sstojos/zynthian-mini/resources/assembled_top.png

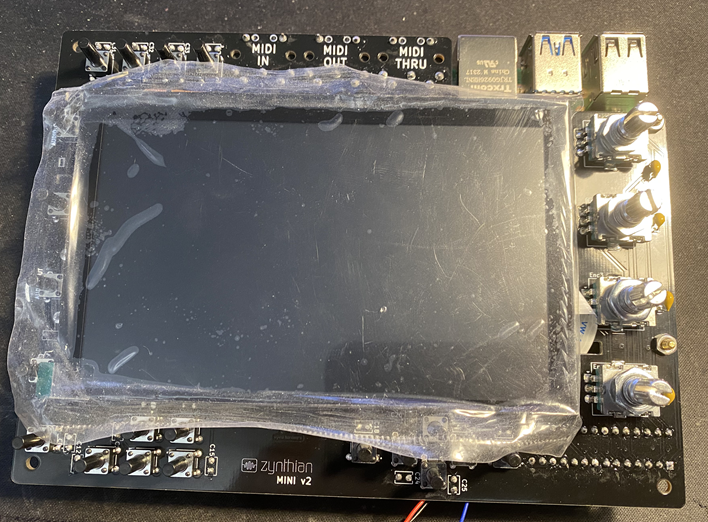
resources/assembled_top.png
