sstojos/zynthian-mini/resources/new-case-layout.png

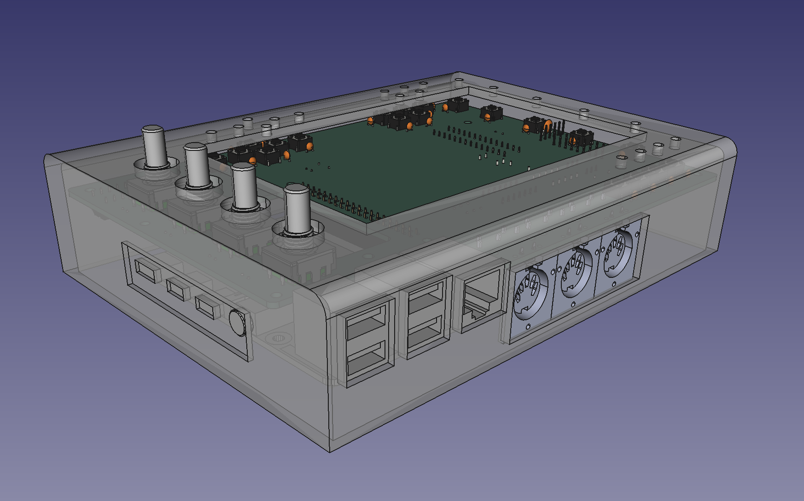
resources/new-case-layout.png
