sstojos/zynthian-mini/resources/PCB-back-with-rpi.png

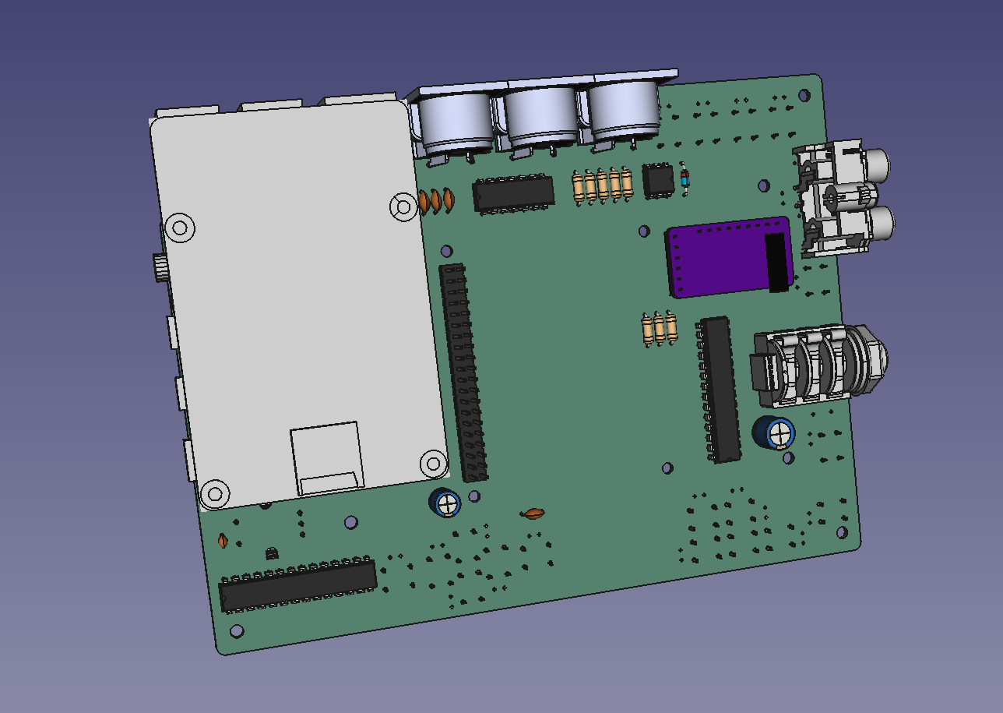
resources/PCB-back-with-rpi.png
