sstojos/zynthian-mini/resources/PCB-back.png

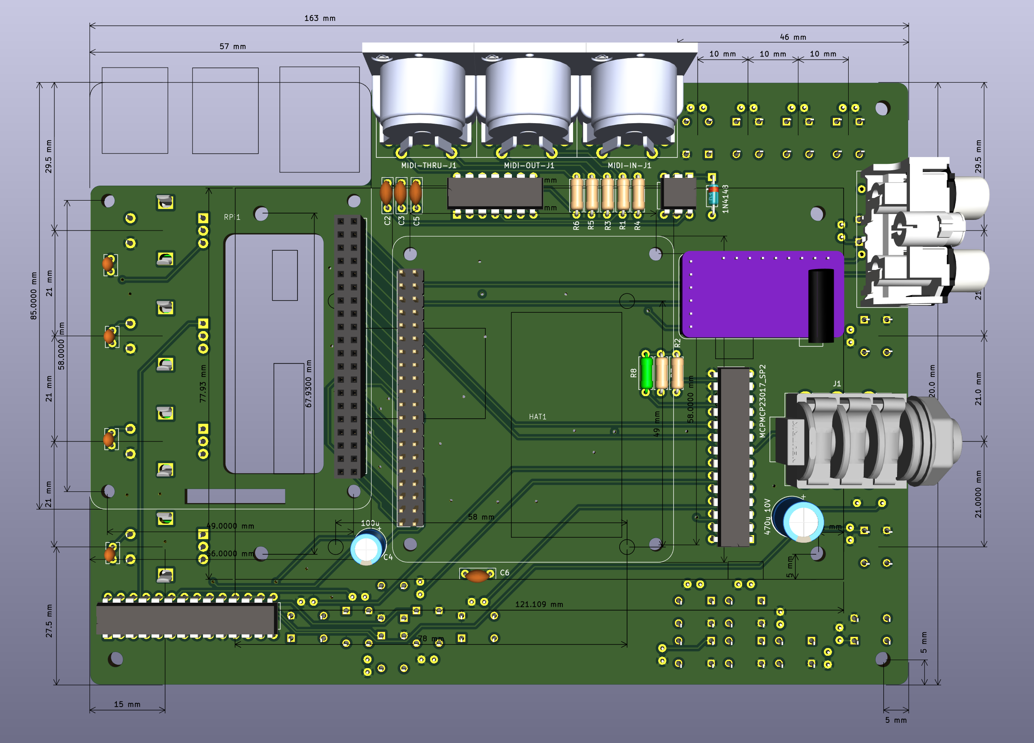
resources/PCB-back.png
