sstojos/zynthian-mini/resources/PCB-front.png

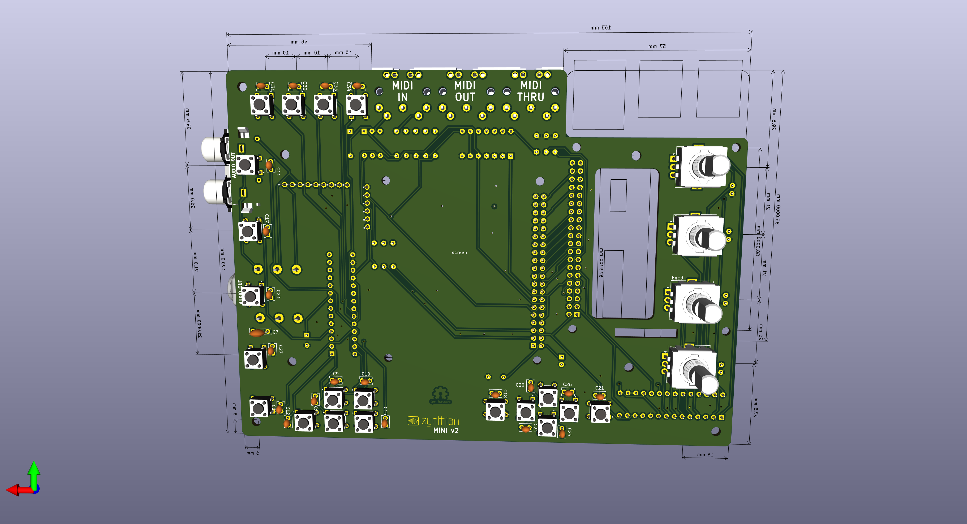
resources/PCB-front.png
