sstojos/zynthian-mini/resources/pcm5102a_circuit_diagram-1.webp

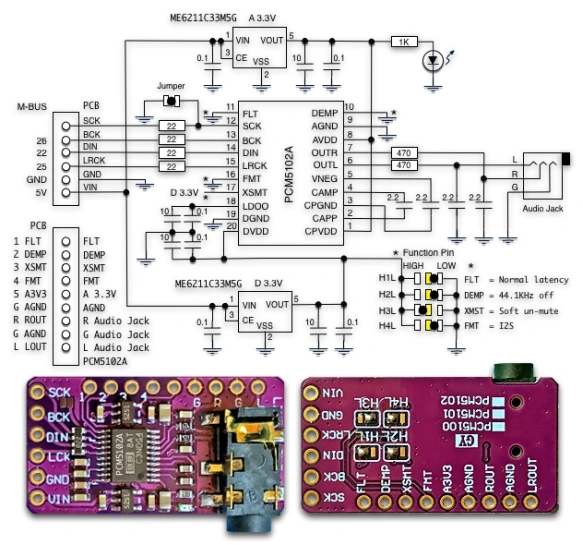
resources/pcm5102a_circuit_diagram-1.webp
