sstojos/zynthian-mini/resources/rpi-cooler.png

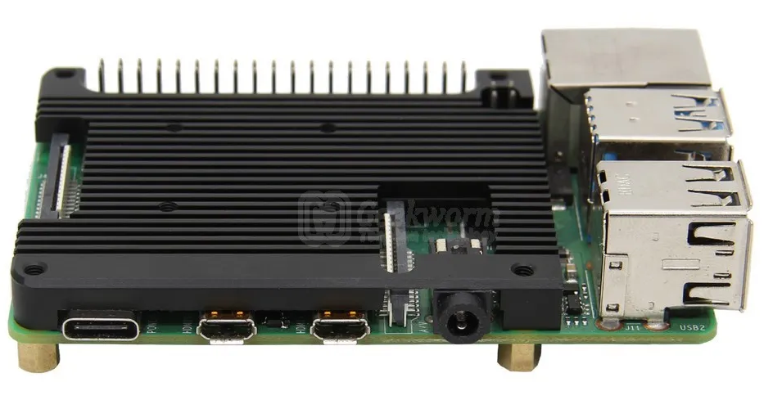
resources/rpi-cooler.png
