sstojos/zynthian-mini/resources/rpi_screen_cable.png

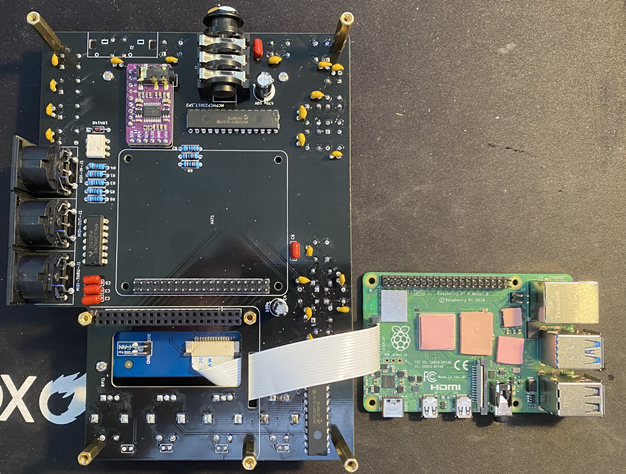
resources/rpi_screen_cable.png
