sstojos/zynthian-mini/resources/screen_cable.png

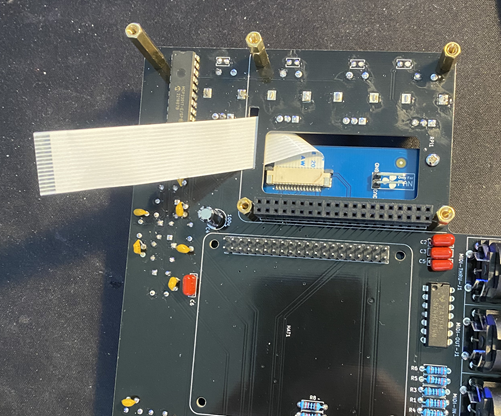
resources/screen_cable.png
