sstojos/zynthian-mini/resources/screen_post_removal.png

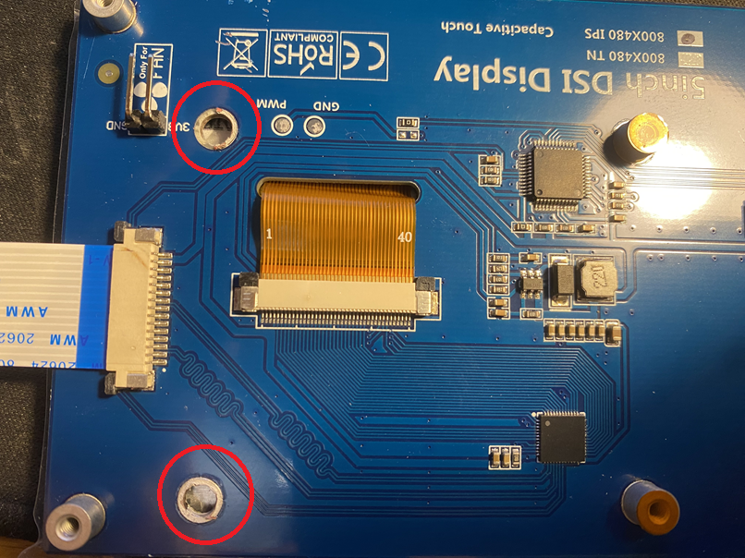
resources/screen_post_removal.png
