sstojos/zynthian-mini/resources/slicer-screenshot-01.png

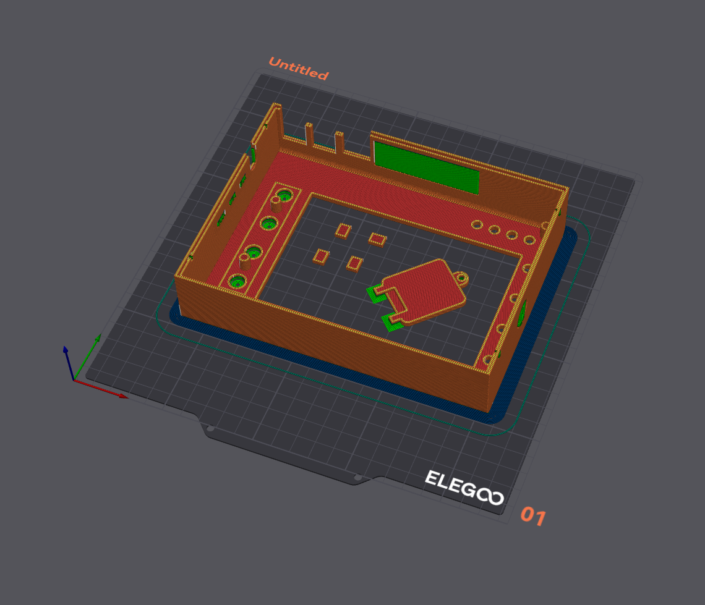
resources/slicer-screenshot-01.png
