sstojos/zynthian-mini/resources/zynthian-on-piano-01.png

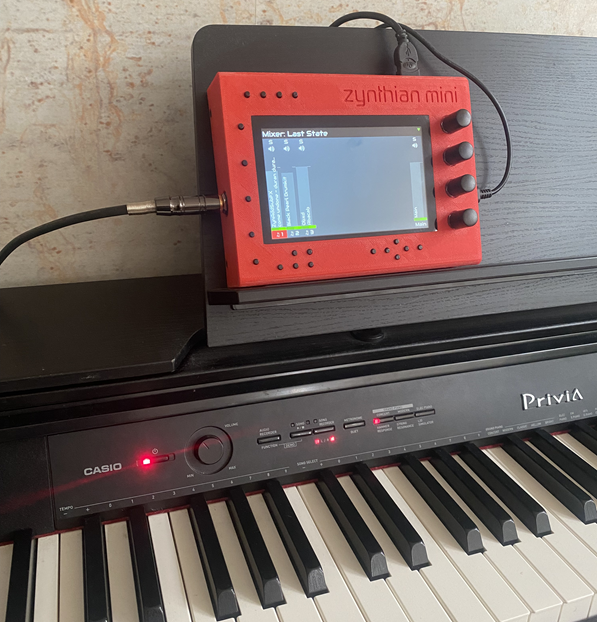
resources/zynthian-on-piano-01.png
