sstojos/zynthian-mini/resources/zynthian-on-piano-02.png

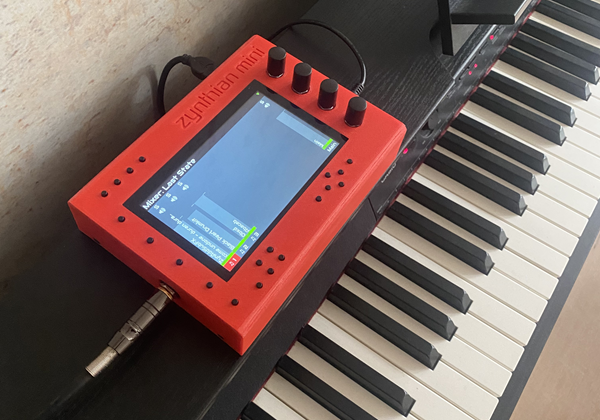
resources/zynthian-on-piano-02.png
