sstojos/zynthian-mini/resources/zynthian_mini_v1_top.png

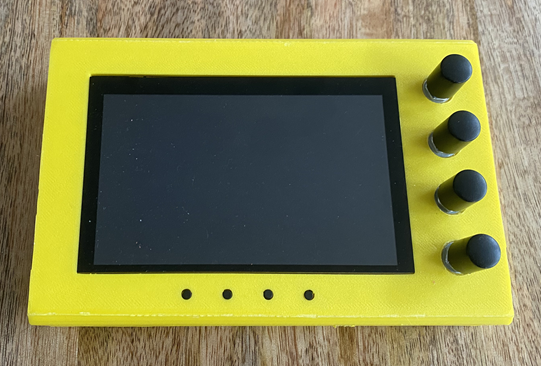
resources/zynthian_mini_v1_top.png
