sstojos/zynthian-mini/resources/zynthian_mini_v2_bottom.png

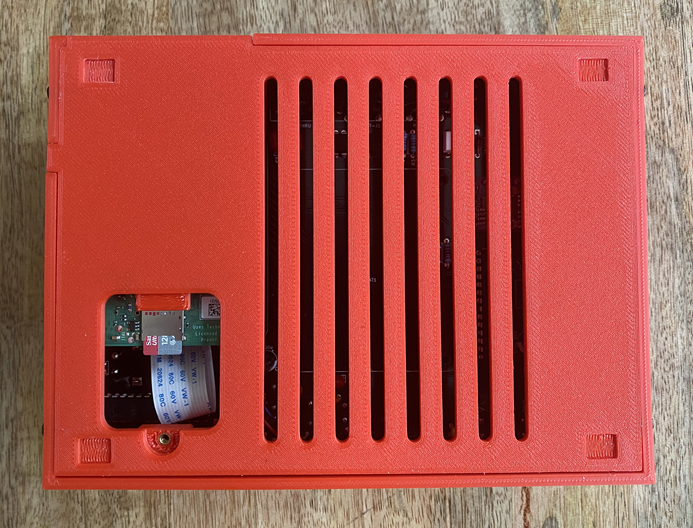
resources/zynthian_mini_v2_bottom.png
