sstojos/zynthian-mini/resources/zynthian_mini_v2_left.png

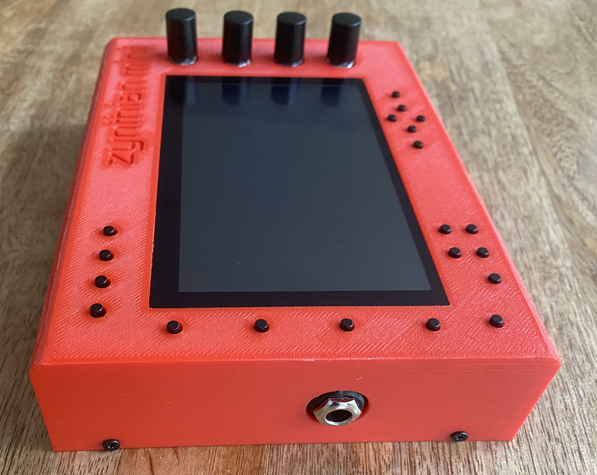
resources/zynthian_mini_v2_left.png
