sstojos/zynthian-mini/resources/zynthian_mini_v2_right.png

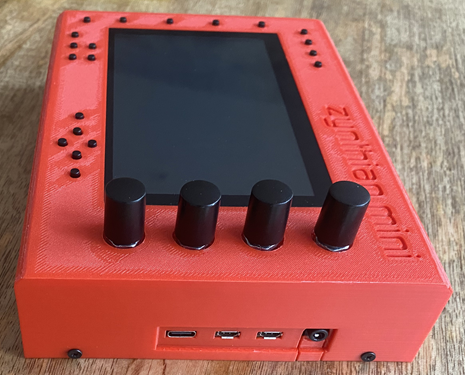
resources/zynthian_mini_v2_right.png
