sstojos/zynthian-mini/resources/components_v2.JPEG

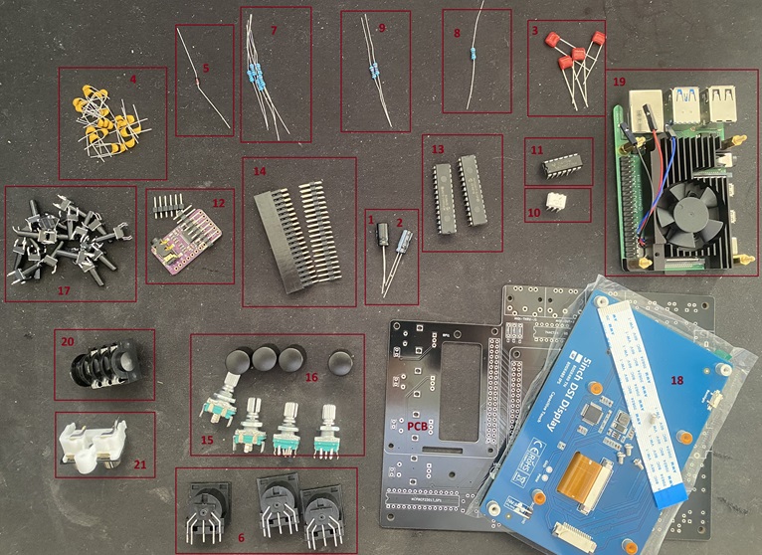
resources/components_v2.JPEG
