sstojos/zynthian-mini/resources/assembled_rear.png

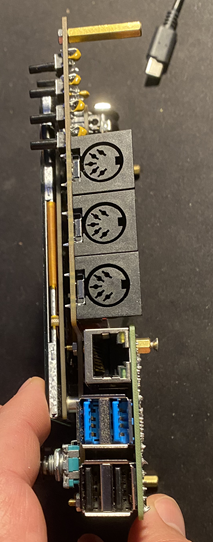
resources/assembled_rear.png
