sstojos/zynthian-mini/resources/assembled_right.png

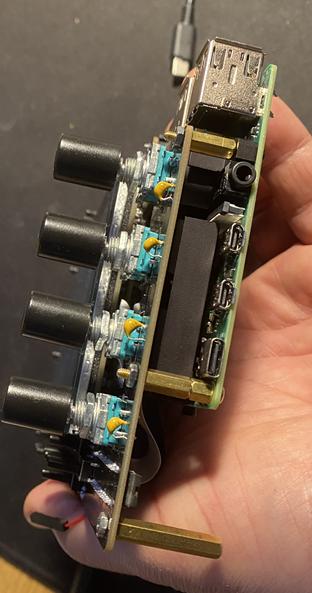
resources/assembled_right.png
