sstojos/zynthian-mini/resources/config-step-01.png

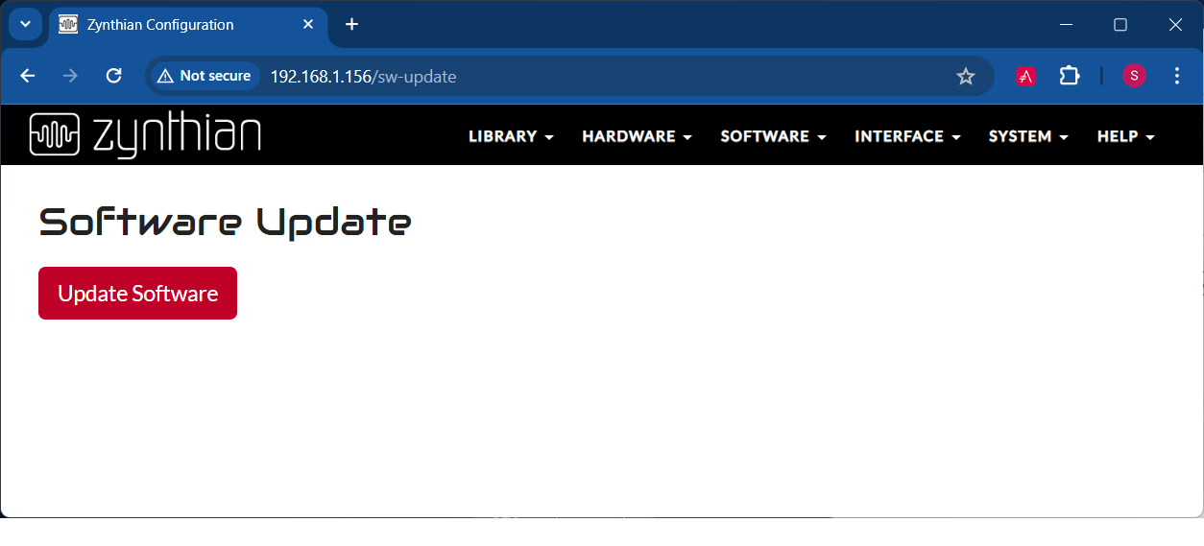
resources/config-step-01.png
