sstojos/zynthian-mini/resources/config-step-02.png

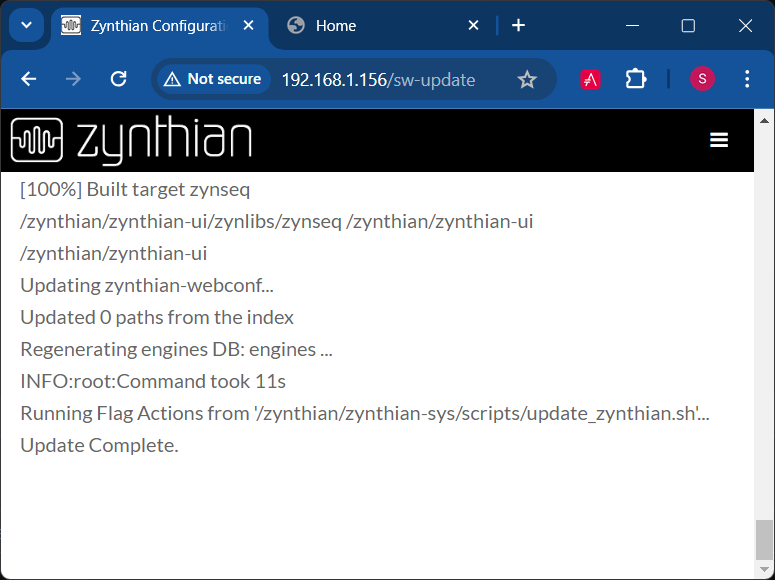
resources/config-step-02.png
