sstojos/zynthian-mini/resources/config-step-04.png

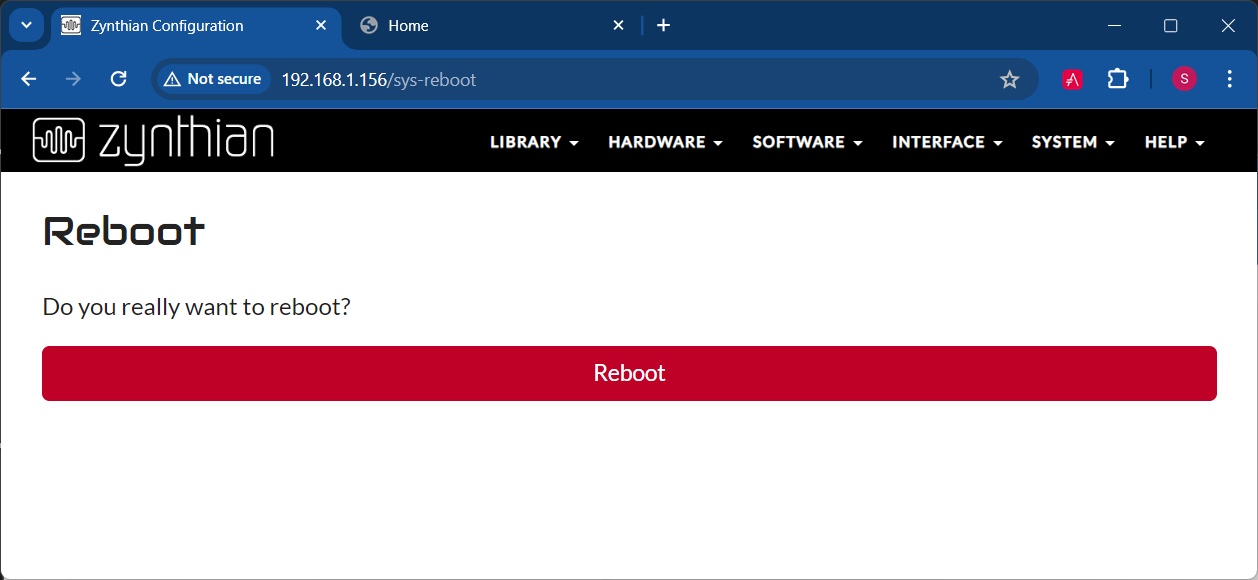
resources/config-step-04.png
