sstojos/zynthian-mini/resources/config-step-05.png

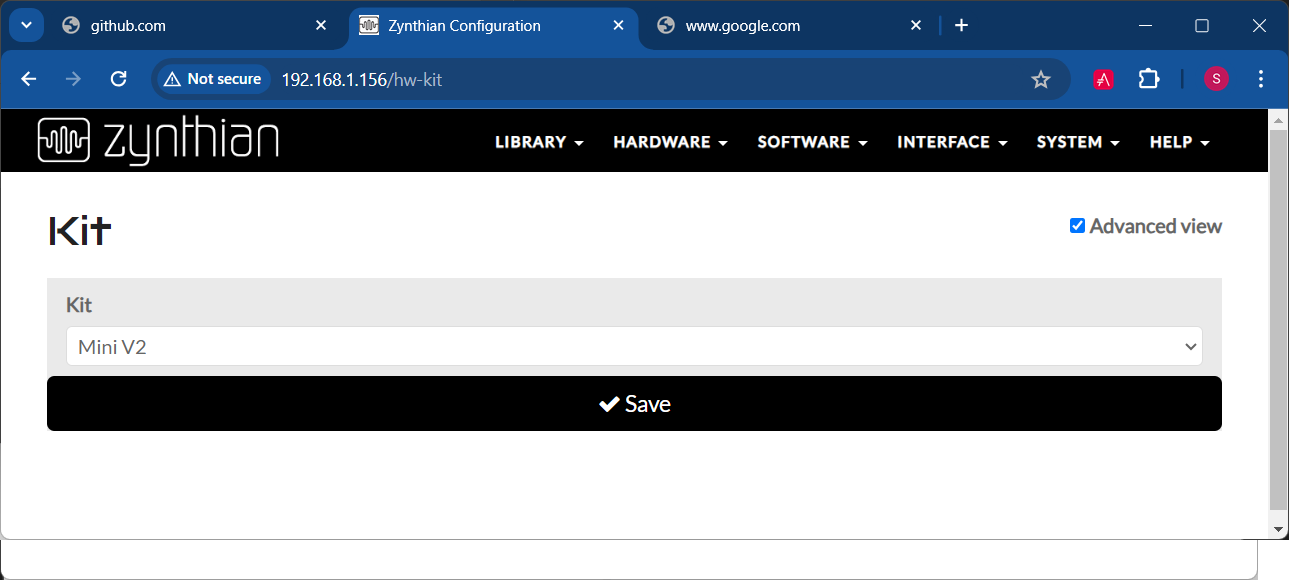
resources/config-step-05.png
