sstojos/zynthian-mini/resources/config-step-06.png

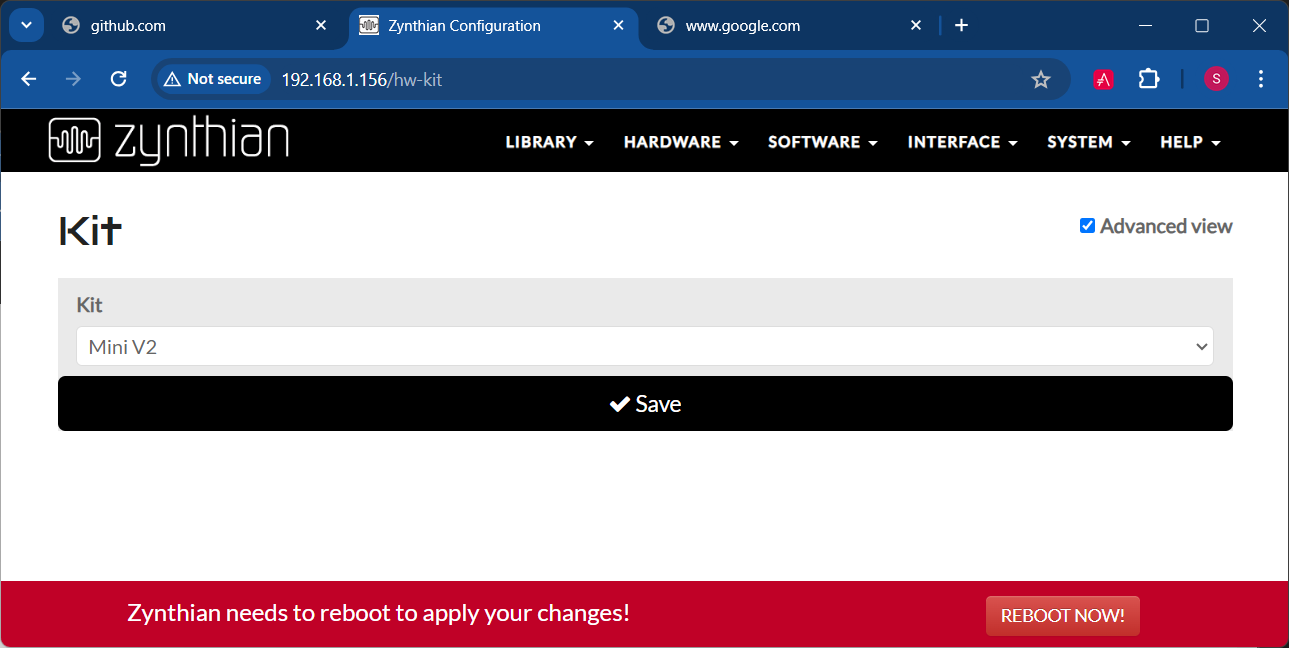
resources/config-step-06.png
