sstojos/zynthian-mini/resources/config-step-07.png

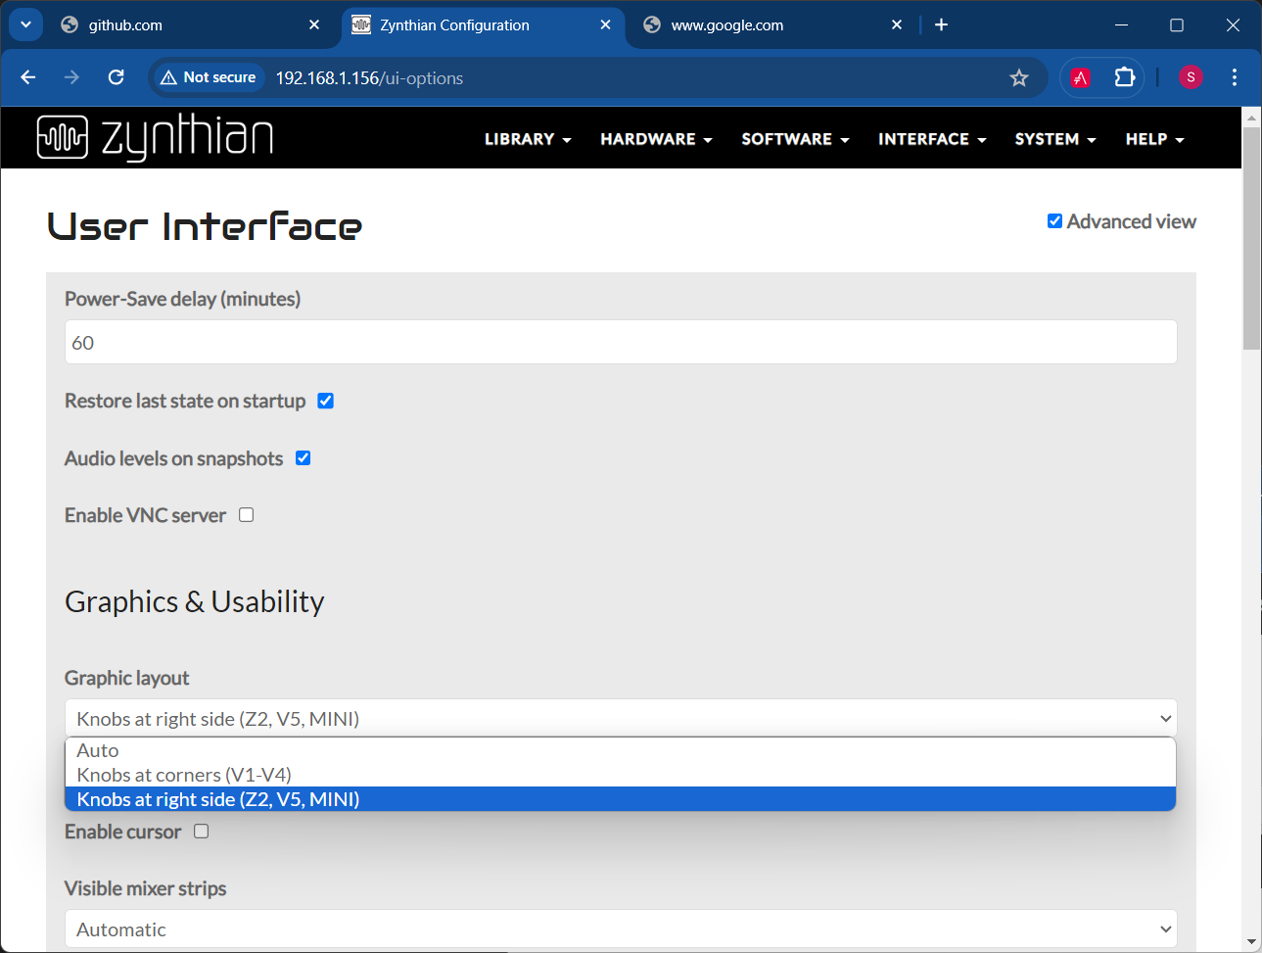
resources/config-step-07.png
