sstojos/zynthian-mini/resources/soldering-step-1.png

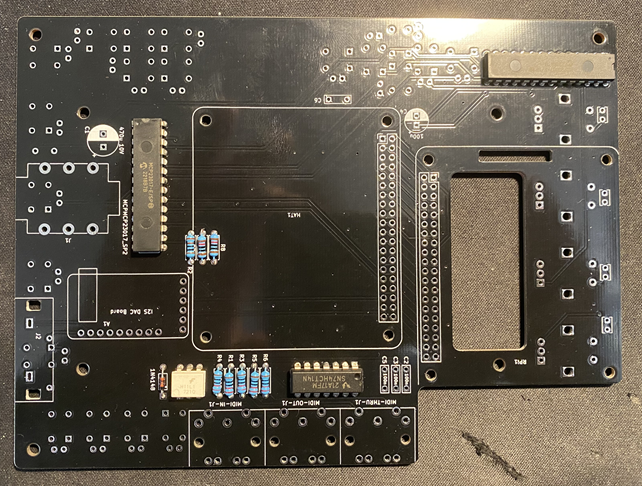
resources/soldering-step-1.png
