sstojos/zynthian-mini/resources/soldering-step-2.png

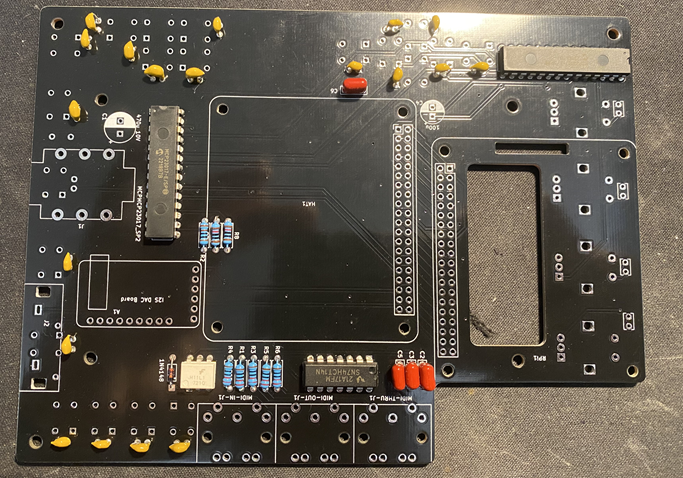
resources/soldering-step-2.png
