sstojos/zynthian-mini/resources/soldering-step-3.png

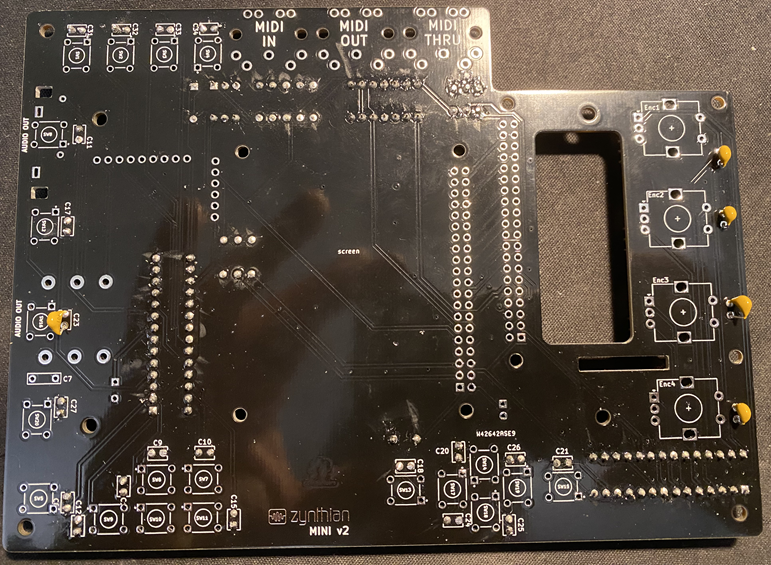
resources/soldering-step-3.png
