sstojos/zynthian-mini/resources/soldering-step-4.png

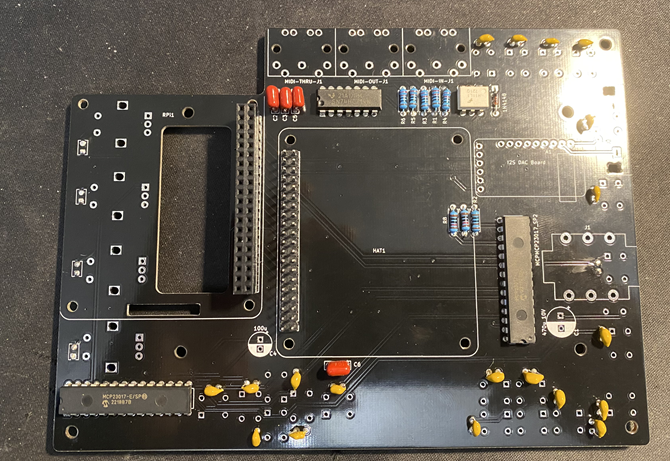
resources/soldering-step-4.png
