sstojos/zynthian-mini/resources/soldering-step-5.png

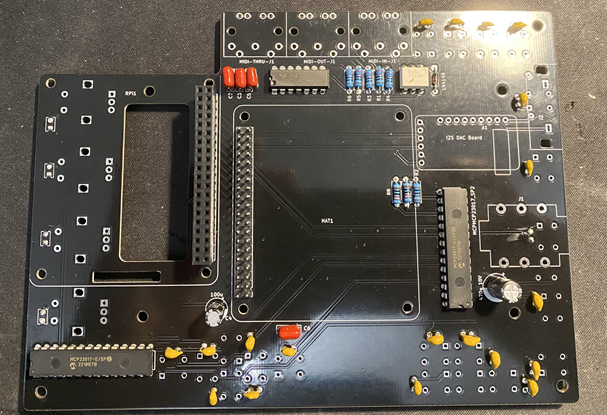
resources/soldering-step-5.png
