sstojos/zynthian-mini/resources/soldering-step-7.png

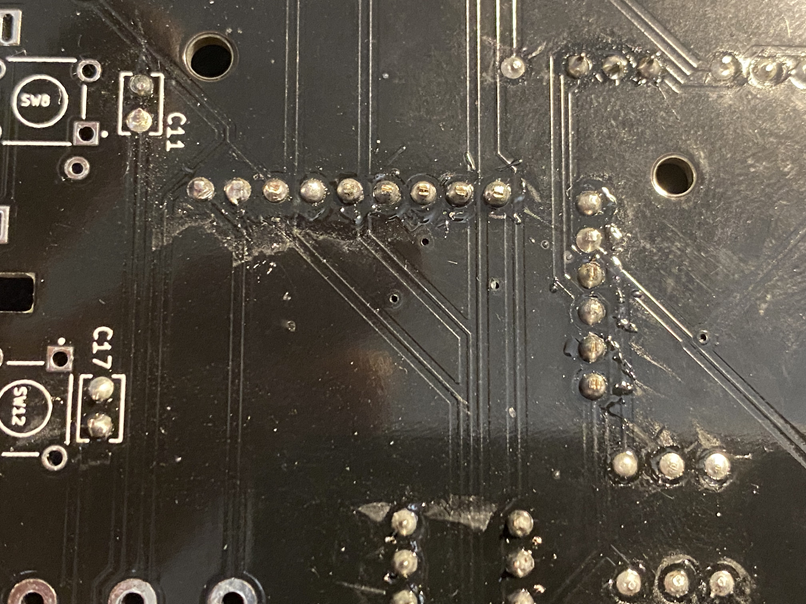
resources/soldering-step-7.png
