sstojos/zynthian-mini/resources/soldering-step-8.png

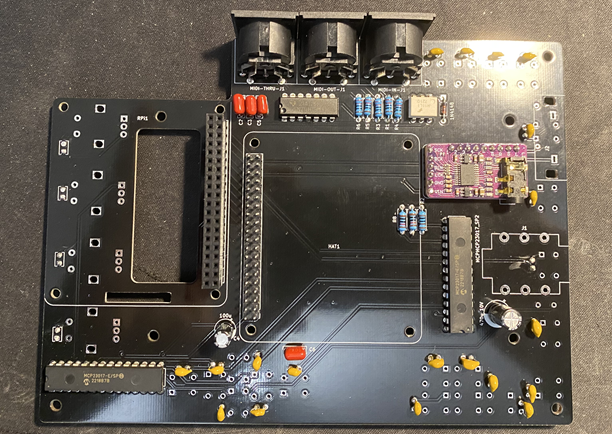
resources/soldering-step-8.png
