sstojos/zynthian-mini/resources/soldering-step-9.png

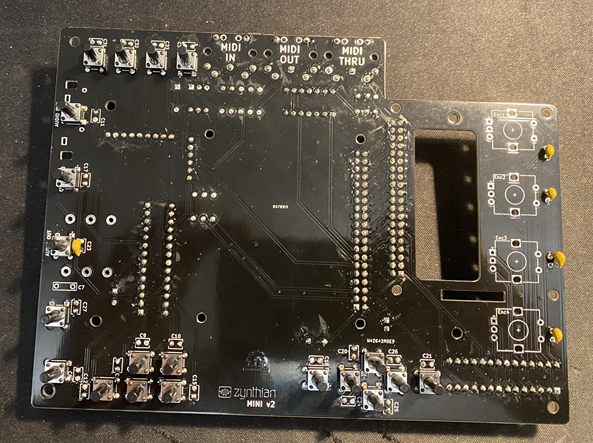
resources/soldering-step-9.png
