sstojos/zynthian-mini/resources/soldering-step-10.png

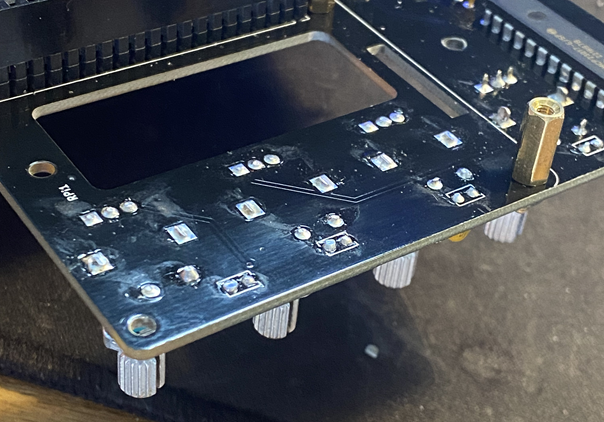
resources/soldering-step-10.png
