sstojos/zynthian-mini/resources/button-evaluation.png

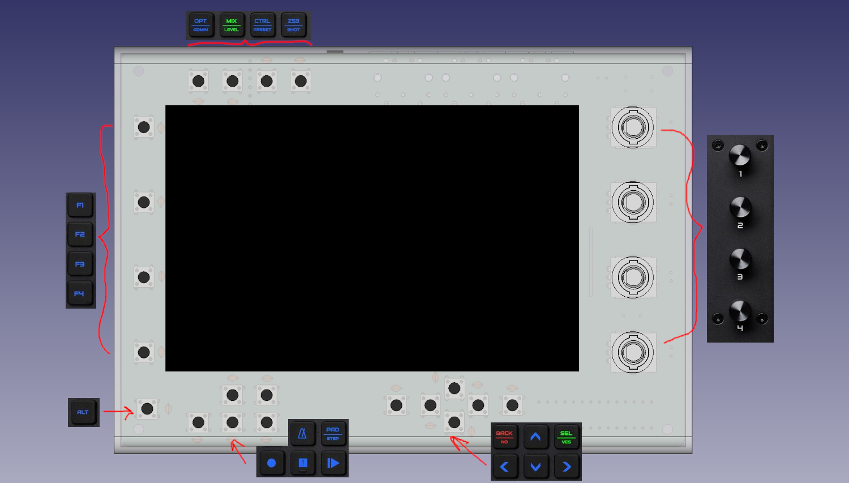
resources/button-evaluation.png
